stetro/AMSRobot/presentation/final/openscad.png

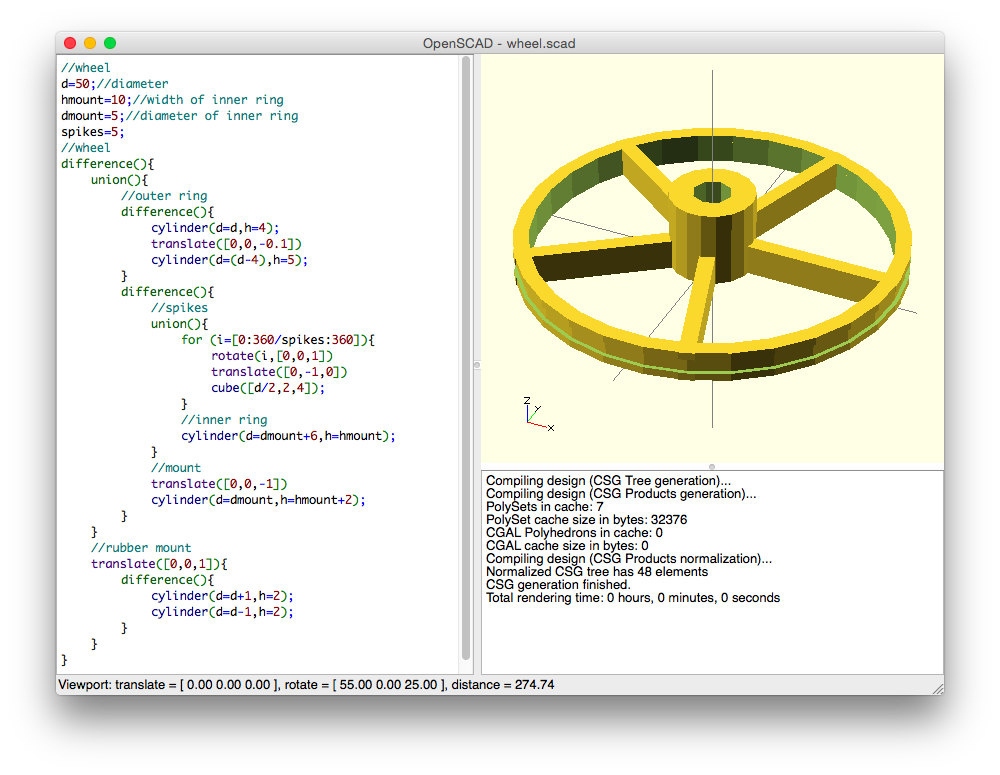
presentation/final/openscad.png
