stetro/AMSRobot/presentation/final/square-hull.png

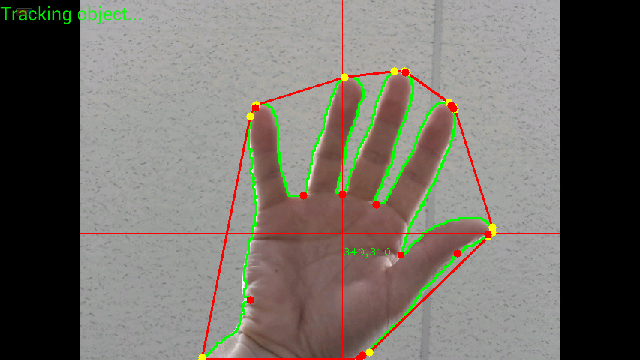
presentation/final/square-hull.png
