stetro/AMSRobot/presentation/final/wlan.png

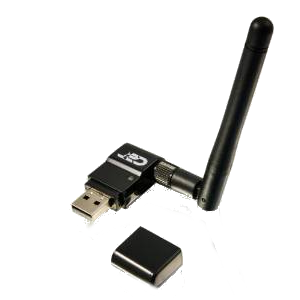
presentation/final/wlan.png
