stetro/AMSRobot/presentation/final/printrbot.png

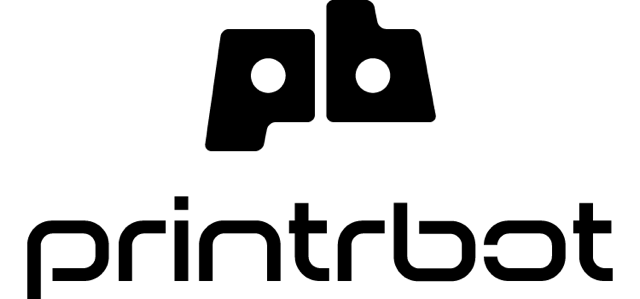
presentation/final/printrbot.png
