stetro/AMSRobot/presentation/final/test2.jpg

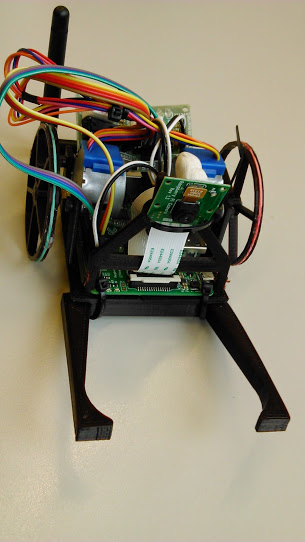
presentation/final/test2.jpg
