stetro/AMSRobot/presentation/final/test.jpg

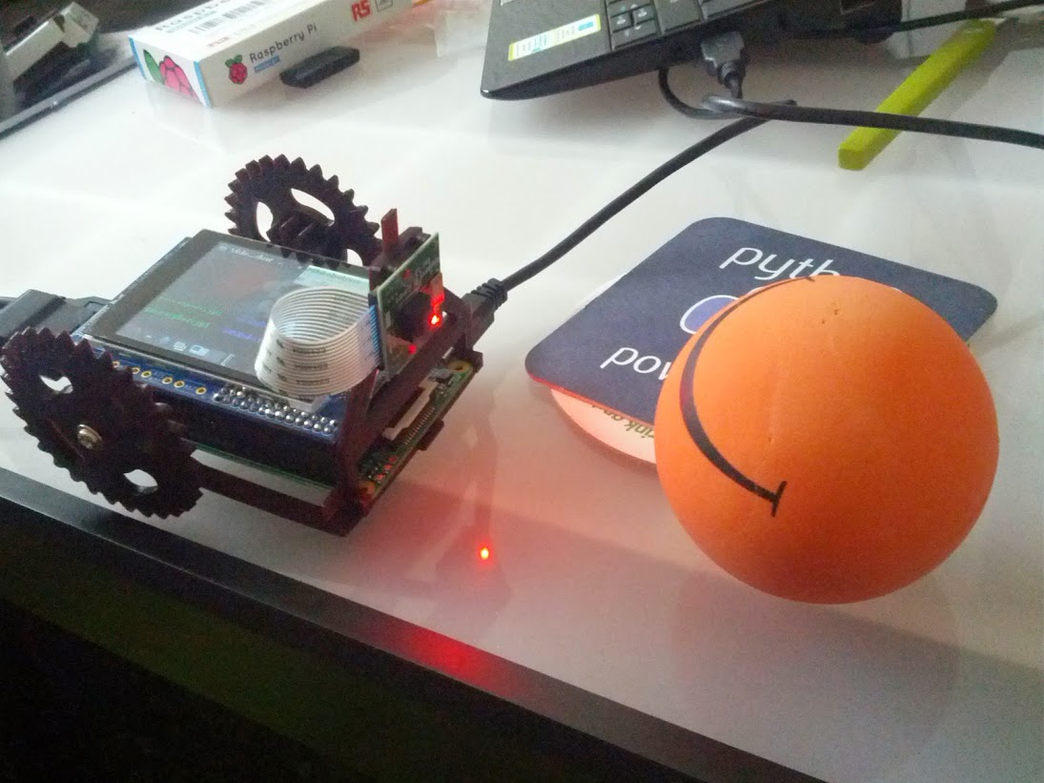
presentation/final/test.jpg
